naman-tanwar/Innovative-Smart-Street-light-system-with-smart-Zebra-crossing/Circuit Smart Zebra.png

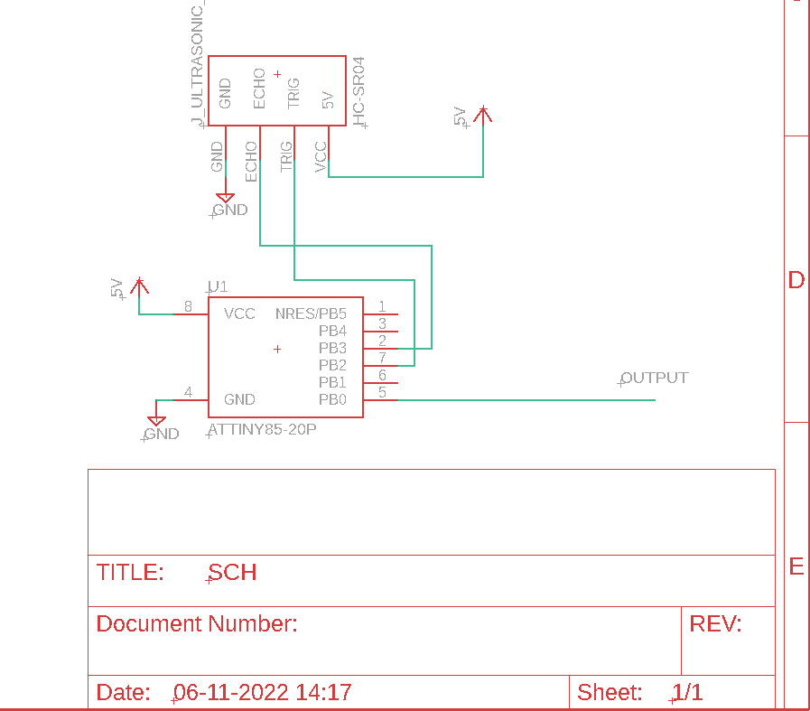
Circuit Smart Zebra.png
