naman-tanwar/Innovative-Smart-Street-light-system-with-smart-Zebra-crossing/Design/Block Design.png

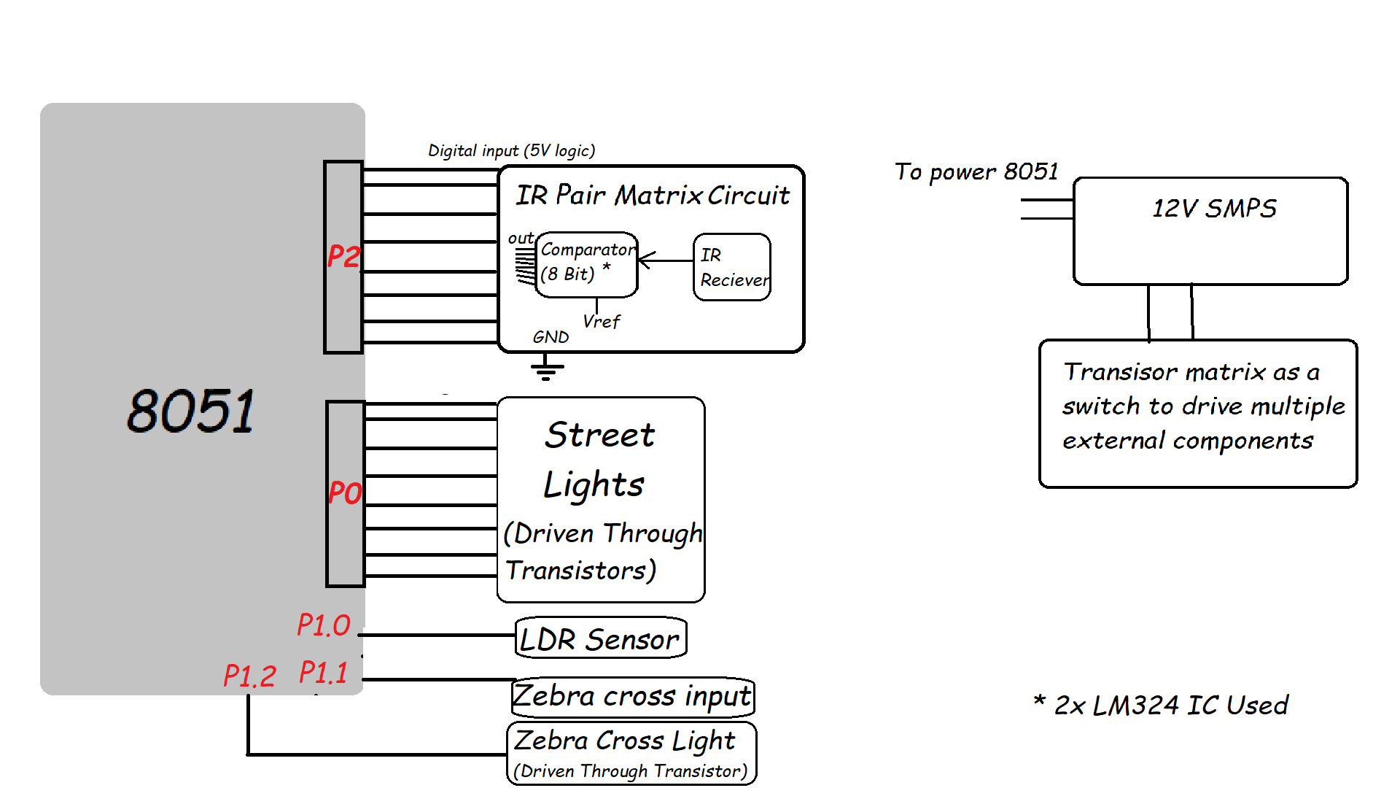
Design/Block Design.png
