naman-tanwar/Innovative-Smart-Street-light-system-with-smart-Zebra-crossing/Design/FrontEnd.png

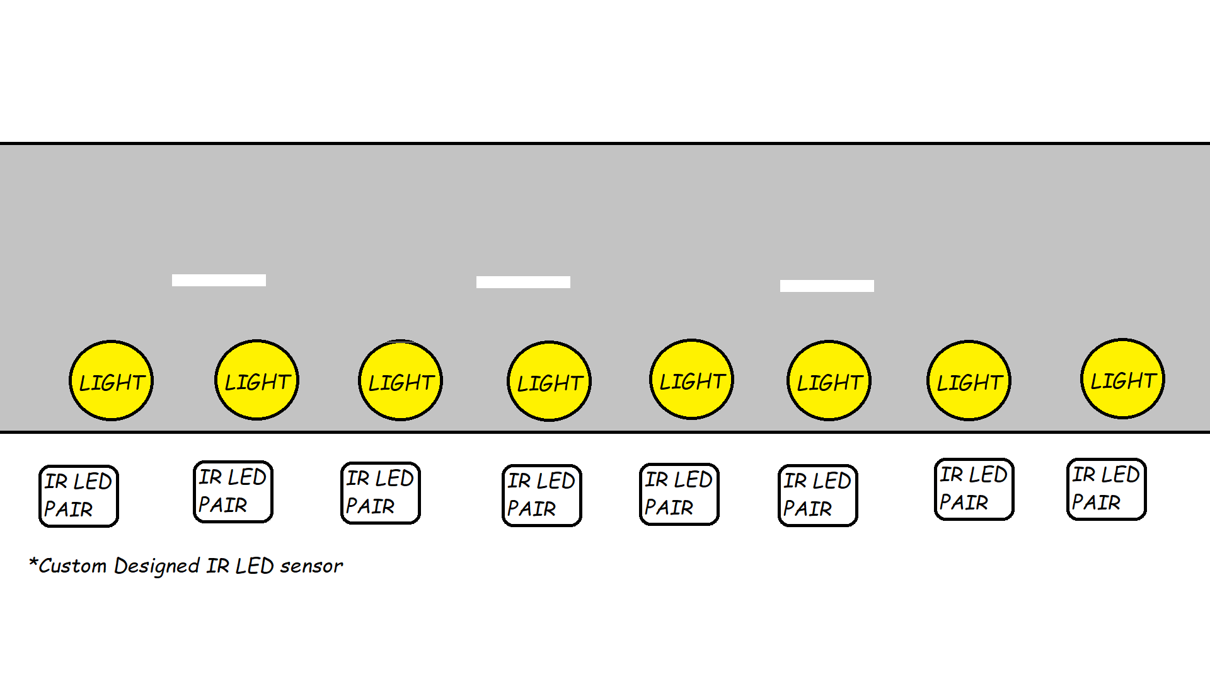
Design/FrontEnd.png
