naman-tanwar/Innovative-Smart-Street-light-system-with-smart-Zebra-crossing/Design/PCB Related/PCB Renders/23-08-22.png

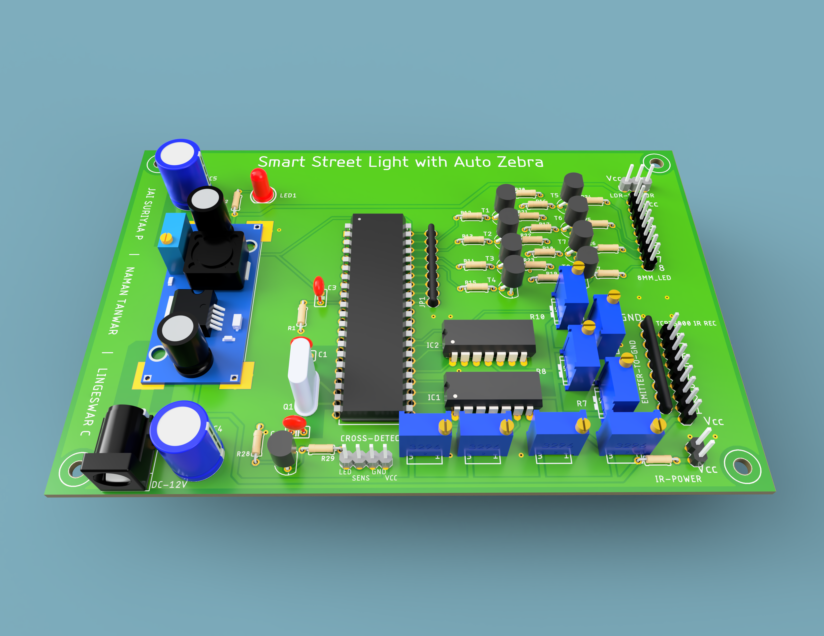
Design/PCB Related/PCB Renders/23-08-22.png
