naman-tanwar/Innovative-Smart-Street-light-system-with-smart-Zebra-crossing/Design/PCB Related/PCB Renders/TOP.png

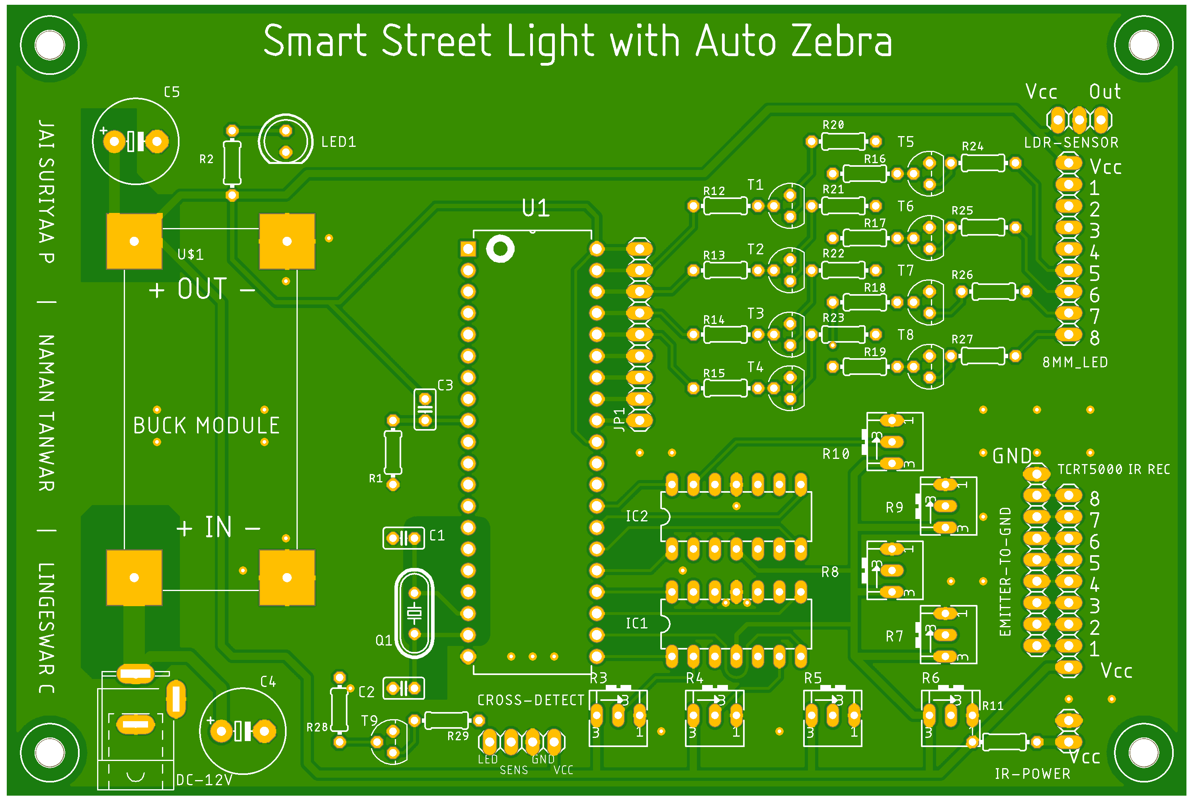
Design/PCB Related/PCB Renders/TOP.png
