naman-tanwar/Innovative-Smart-Street-light-system-with-smart-Zebra-crossing/Main 8051 based Circuit.png

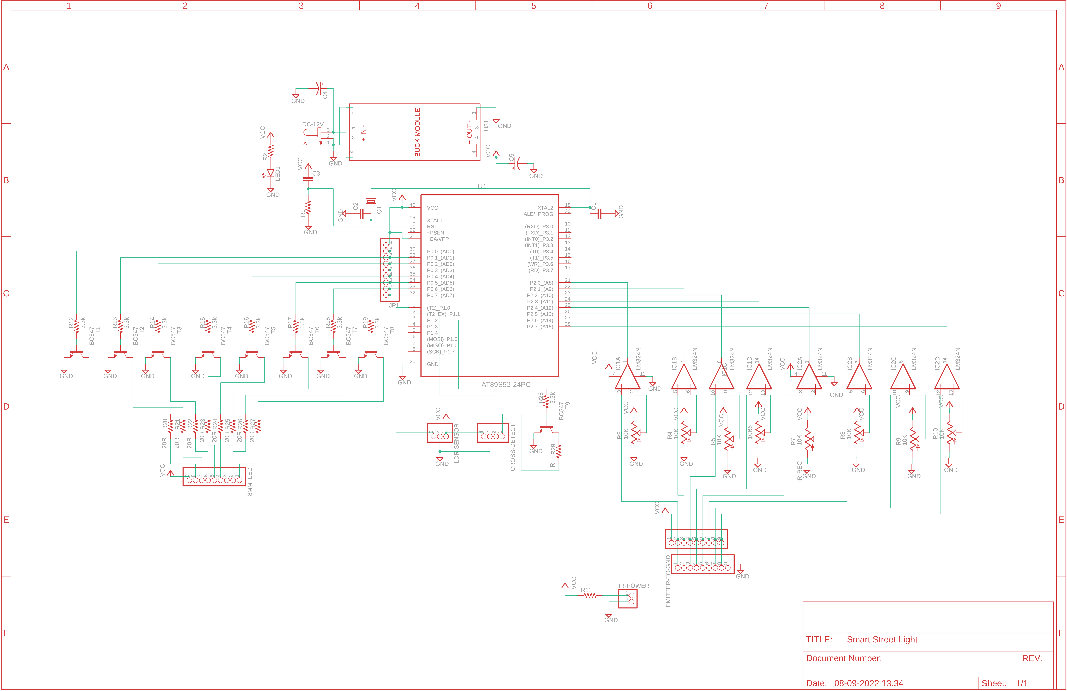
Main 8051 based Circuit.png
