naman-tanwar/Innovative-Smart-Street-light-system-with-smart-Zebra-crossing/Design/PCB Related/Eagle 3d files/40P6_ATM.step

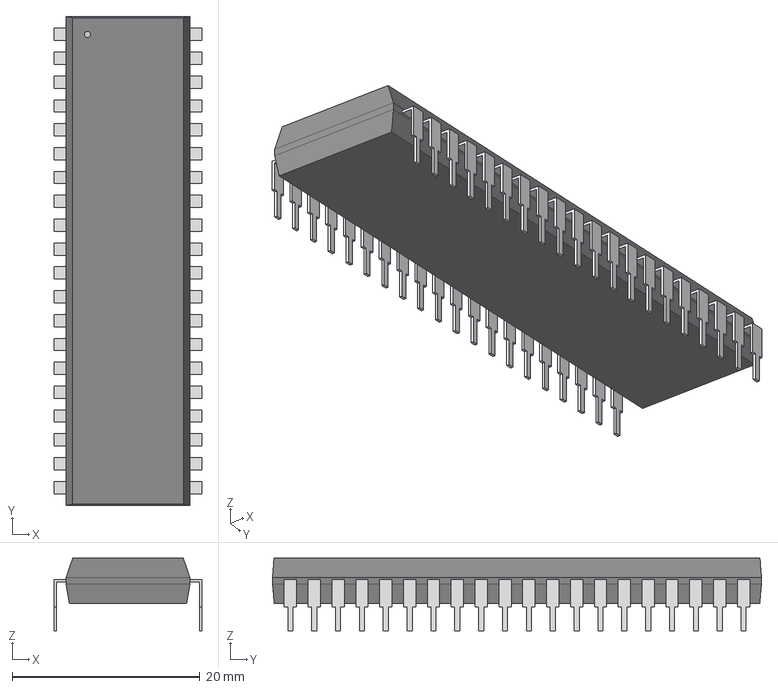
[picture p45: CAD file, 2022-11-11]
Design/PCB Related/Eagle 3d files/40P6_ATM.step
15.7 x 52.1 x 7.75 mm
