naman-tanwar/Innovative-Smart-Street-light-system-with-smart-Zebra-crossing/Design/3D and Laser Cut Designs/RENDERS/ASSEMBLY3.png

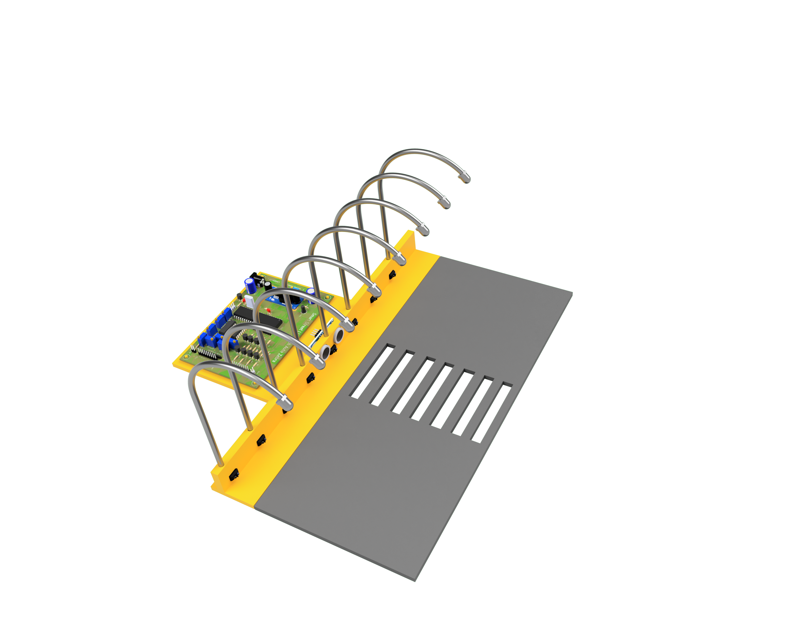
Design/3D and Laser Cut Designs/RENDERS/ASSEMBLY3.png
