naman-tanwar/Innovative-Smart-Street-light-system-with-smart-Zebra-crossing/Design/3D and Laser Cut Designs/RENDERS/ASSEMBLY.png

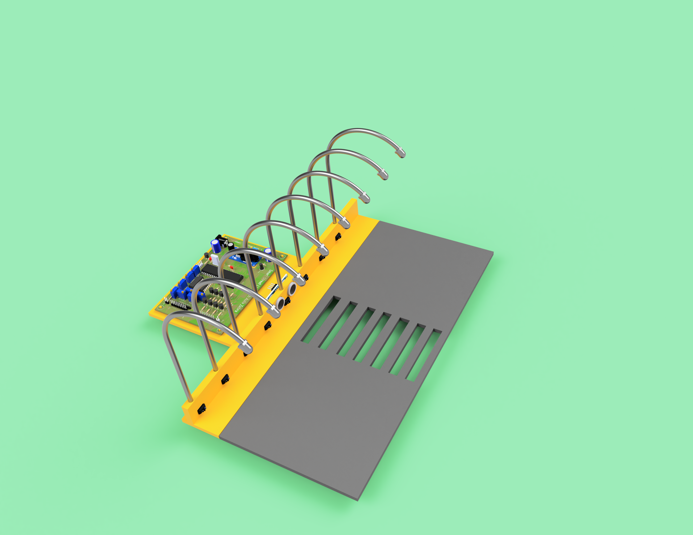
Design/3D and Laser Cut Designs/RENDERS/ASSEMBLY.png
