naman-tanwar/Innovative-Smart-Street-light-system-with-smart-Zebra-crossing/Design/3D and Laser Cut Designs/RENDERS/Assembly_with_support_2022-Aug-28_08-04-34AM-000_CustomizedView6097944497_png.png

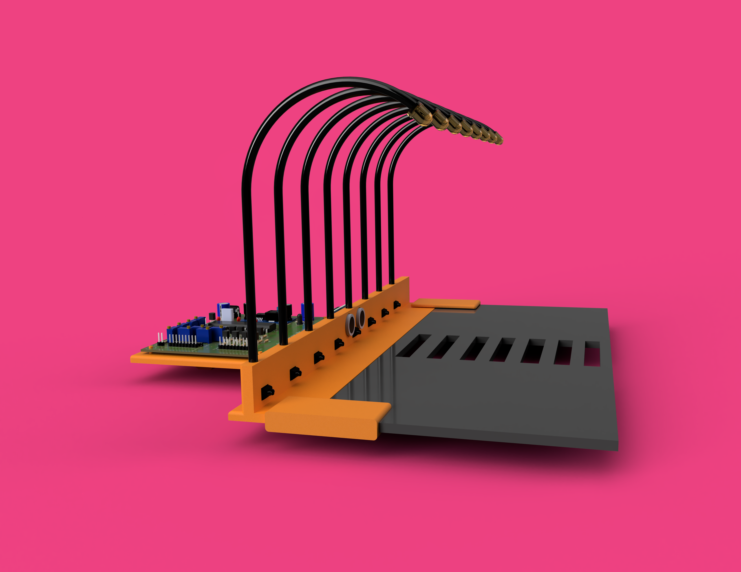
Design/3D and Laser Cut Designs/RENDERS/Assembly_with_support_2022-Aug-28_08-04-34AM-000_CustomizedView6097944497_png.png
