naman-tanwar/Innovative-Smart-Street-light-system-with-smart-Zebra-crossing/Design/3D and Laser Cut Designs/RENDERS/Assembly_with_support_2022-Aug-28alpha.png

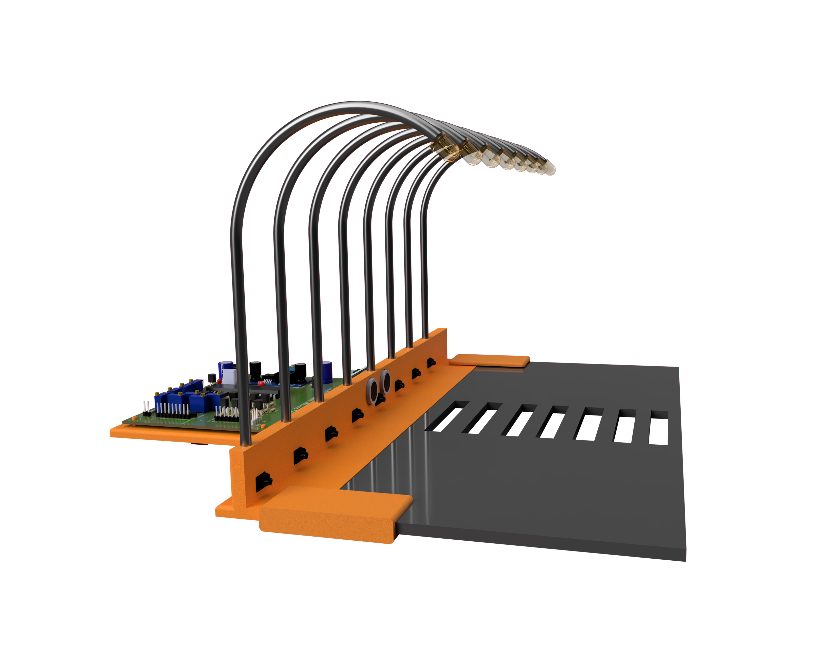
Design/3D and Laser Cut Designs/RENDERS/Assembly_with_support_2022-Aug-28alpha.png
